MW-1007/WordClockMiniV4/include/wordclock_font.h

#pragma once
#include <Arduino.h>

// Generated from: WordClock.woff2 (5104 bytes)
const uint8_t wordclock_woff2[] PROGMEM = {
  0x77, 0x4F, 0x46, 0x32, 0x00, 0x01, 0x00, 0x00, 0x00, 0x00, 0x13, 0xF0, 0x00, 0x0F, 0x00, 0x00,
  0x00, 0x00, 0x2E, 0xE4, 0x00, 0x00, 0x13, 0x91, 0x00, 0x01, 0x00, 0x00, 0x00, 0x00, 0x00, 0x00,
  0x00, 0x00, 0x00, 0x00, 0x00, 0x00, 0x00, 0x00, 0x00, 0x00, 0x00, 0x00, 0x00, 0x00, 0x00, 0x00,
  0x3F, 0x46, 0x46, 0x54, 0x4D, 0x1C, 0x1A, 0x18, 0x1B, 0x8B, 0x70, 0x1C, 0x30, 0x06, 0x60, 0x00,
  0x83, 0x36, 0x11, 0x08, 0x0A, 0xB8, 0x28, 0xA9, 0x17, 0x0B, 0x81, 0x58, 0x00, 0x01, 0x36, 0x02,
  0x24, 0x03, 0x83, 0x2C, 0x04, 0x20, 0x05, 0x8A, 0x2E, 0x07, 0x82, 0x1C, 0x1B, 0x78, 0x25, 0x55,
  0x46, 0x86, 0x8D, 0x03, 0x30, 0xF1, 0x68, 0x97, 0x88, 0xA8, 0xDA, 0x8C, 0x11, 0xFC, 0x7F, 0x9D,
  0xBC, 0x31, 0xF5, 0x43, 0xDD, 0x52, 0x50, 0x63, 0x28, 0x63, 0x88, 0x86, 0x82, 0x2D, 0x86, 0xB1,
  0x0A, 0x48, 0x43, 0x53, 0x38, 0x36, 0x92, 0x42, 0x0E, 0x04, 0x21, 0x07, 0x79, 0xF6, 0xDF, 0x0E,
  0x78, 0x85, 0x57, 0xD7, 0x7A, 0x67, 0xC1, 0x03, 0x1F, 0x2E, 0xBE, 0x1B, 0x15, 0x3F, 0xC2, 0x01,
  0xBB, 0xDF, 0xF2, 0xBD, 0x23, 0x34, 0xF6, 0x49, 0xAE, 0x0F, 0xCF, 0xCF, 0xE9, 0x9F, 0xFB, 0xDE,
  0x23, 0x88, 0x55, 0x34, 0x95, 0x84, 0x7C, 0x46, 0x13, 0xA0, 0x12, 0x08, 0x78, 0x94, 0xA0, 0xD1,
  0x86, 0x24, 0x58, 0x82, 0x95, 0x22, 0x15, 0x0A, 0x33, 0xEC, 0xDD, 0xE0, 0xBF, 0xA3, 0xA6, 0x42,
  0x32, 0x51, 0xC3, 0x26, 0x0A, 0x5D, 0x37, 0x67, 0x82, 0xC5, 0x4E, 0x93, 0x51, 0x3A, 0xCB, 0x27,
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
  0x53, 0x92, 0x2D, 0x60, 0x0F, 0x38, 0x43, 0x05, 0xA9, 0x0A, 0x13, 0x8A, 0x52, 0x14, 0xA7, 0x71,
  0x65, 0xE0, 0xA4, 0x27, 0xA8, 0x22, 0xC5, 0x09, 0xAE, 0x48, 0x00, 0x69, 0x24, 0x36, 0xA2, 0x88,
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
};
const size_t wordclock_woff2_len = 5104;
